WRansohoff/STM32WB55Cx_minimal/firmware/usb_vsp/src/main.h

#ifndef _VVC_MAIN_H
#define _VVC_MAIN_H

// Project includes.
#include "global.h"

// Pre-defined memory locations for program initialization.
extern uint32_t _sidata, _sdata, _edata, _sbss, _ebss;

#endif
